Khainguyen1349/1x10_PatchArray_RotmanLens/Figures/ArrayFactor_0deg.png

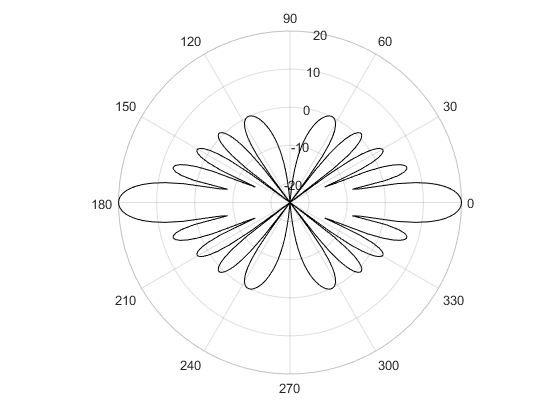
Figures/ArrayFactor_0deg.png
