Khainguyen1349/1x10_PatchArray_RotmanLens/Figures/ElementPattern.png

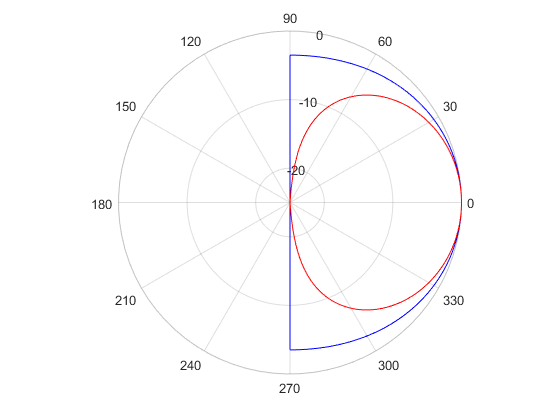
Figures/ElementPattern.png
