Khainguyen1349/1x10_PatchArray_RotmanLens/Figures/Rotman/AF0deg2.png

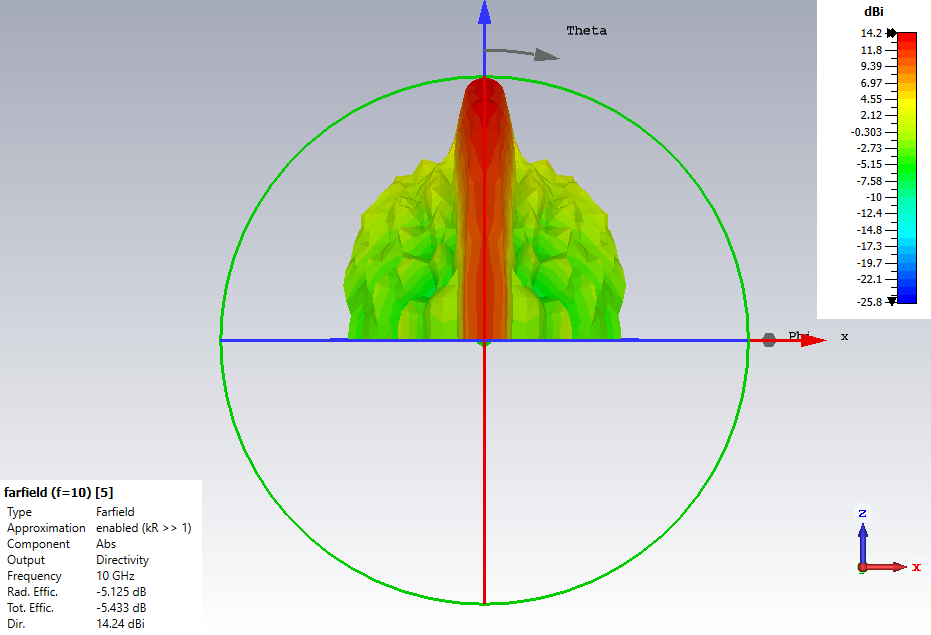
Figures/Rotman/AF0deg2.png
