Khainguyen1349/1x10_PatchArray_RotmanLens/Figures/Rotman/Port1.png

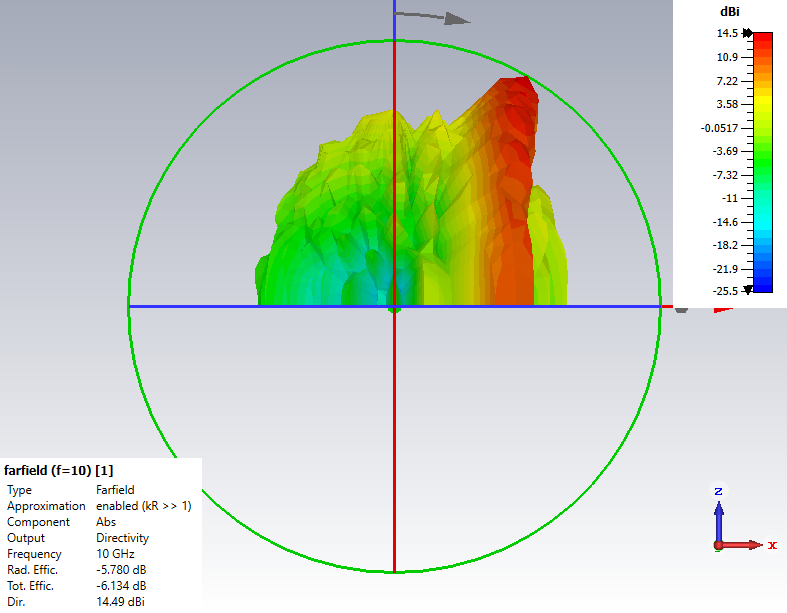
Figures/Rotman/Port1.png
